sigfredonin/Z80-John-Bell-80-280/image/2732_pinout.png

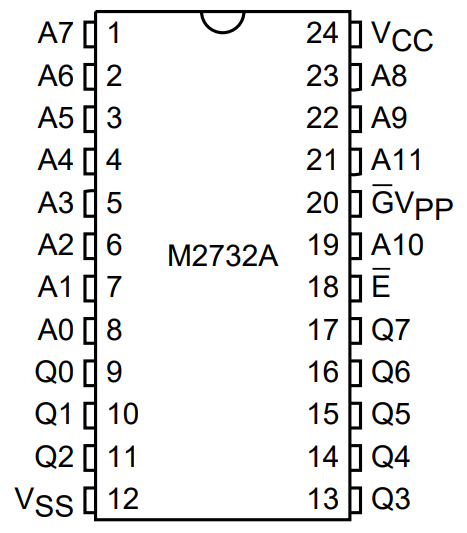
image/2732_pinout.png
