sigfredonin/Z80-John-Bell-80-280/image/7404 Inverter Response to RC Input Circuit.jpg

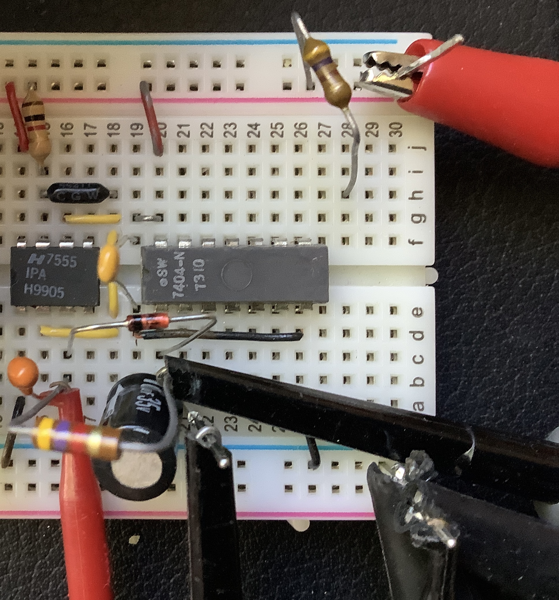
image/7404 Inverter Response to RC Input Circuit.jpg
