sigfredonin/Z80-John-Bell-80-280/image/CD4049AE CMOS Inverter Buffer Response to RC Input.jpg

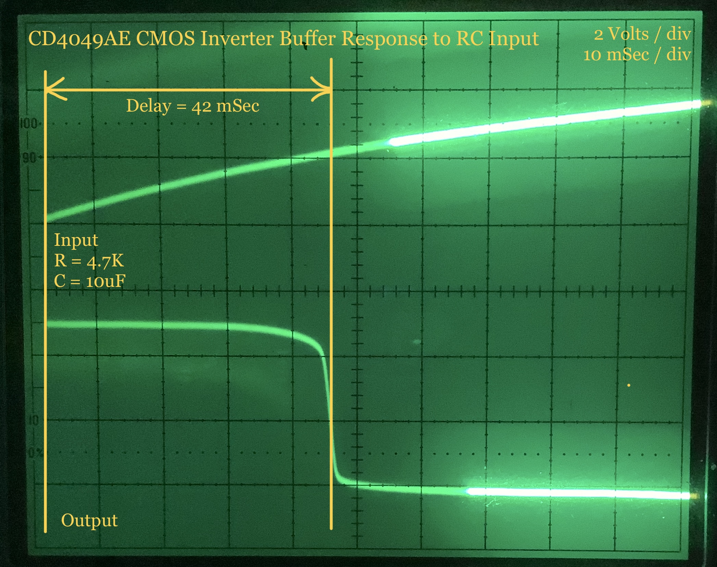
image/CD4049AE CMOS Inverter Buffer Response to RC Input.jpg
