sigfredonin/Z80-John-Bell-80-280/image/EPROM_2716_Reader_schematic.png

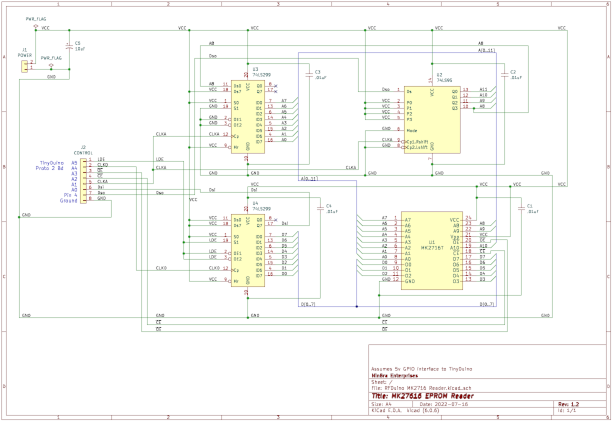
image/EPROM_2716_Reader_schematic.png
