sigfredonin/Z80-John-Bell-80-280/image/John Bell 555 Timer Reset Circuit Response to RC Curve.jpg

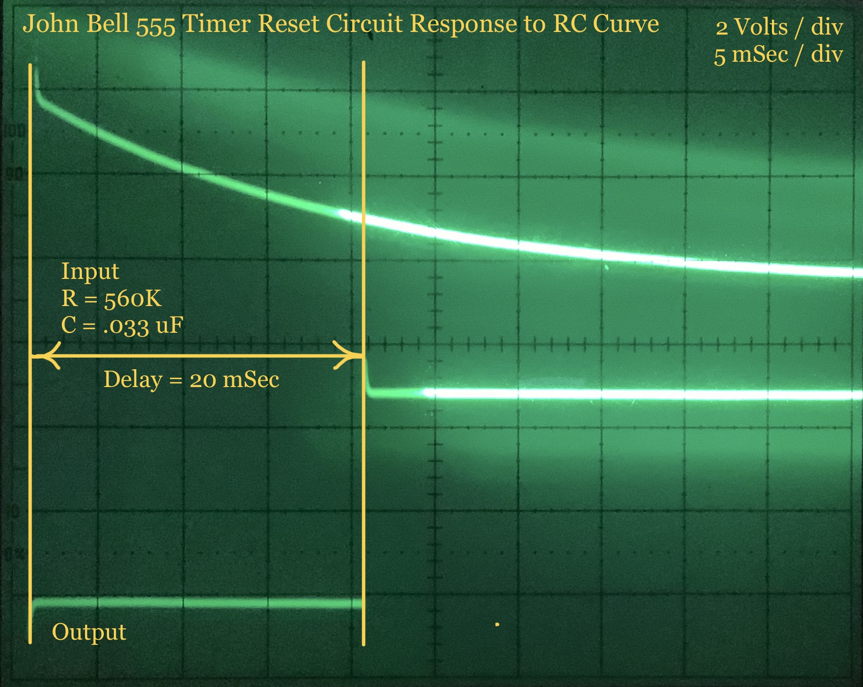
image/John Bell 555 Timer Reset Circuit Response to RC Curve.jpg
