sigfredonin/Z80-John-Bell-80-280/image/Power On Reset - annotated.jpg

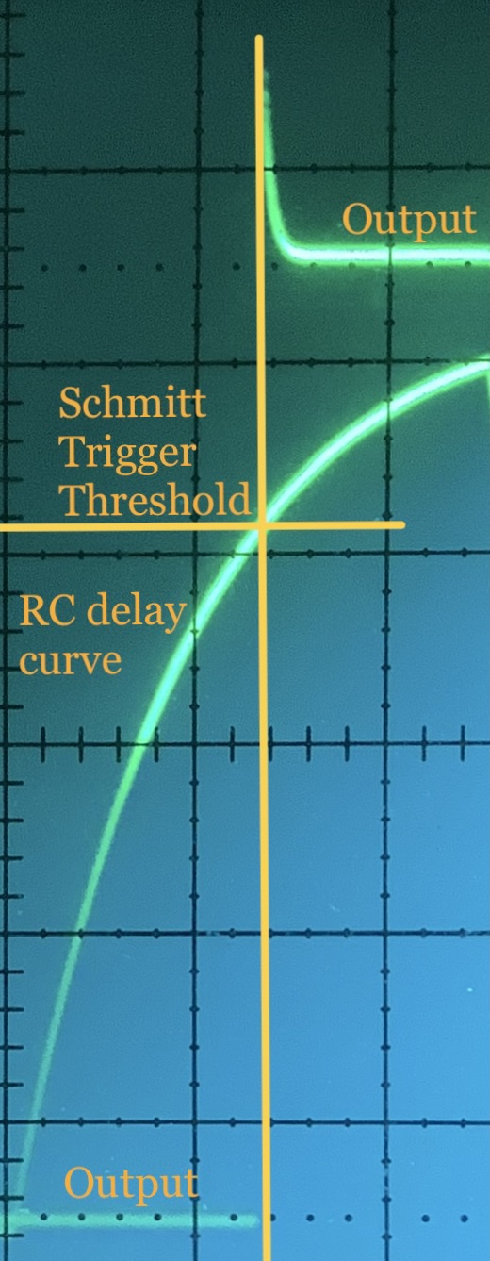
image/Power On Reset - annotated.jpg
