sigfredonin/Z80-John-Bell-80-280/image/TinyDuino 2114 RAM_bb.png

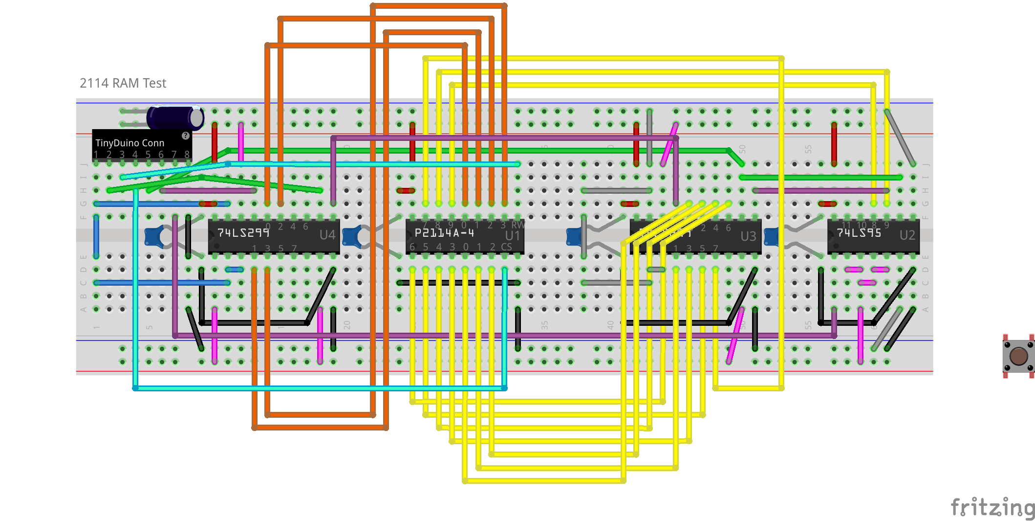
image/TinyDuino 2114 RAM_bb.png
