sigfredonin/Z80-John-Bell-80-280/image/TinyDuino Mk2716 Reader_bb_1.1.png

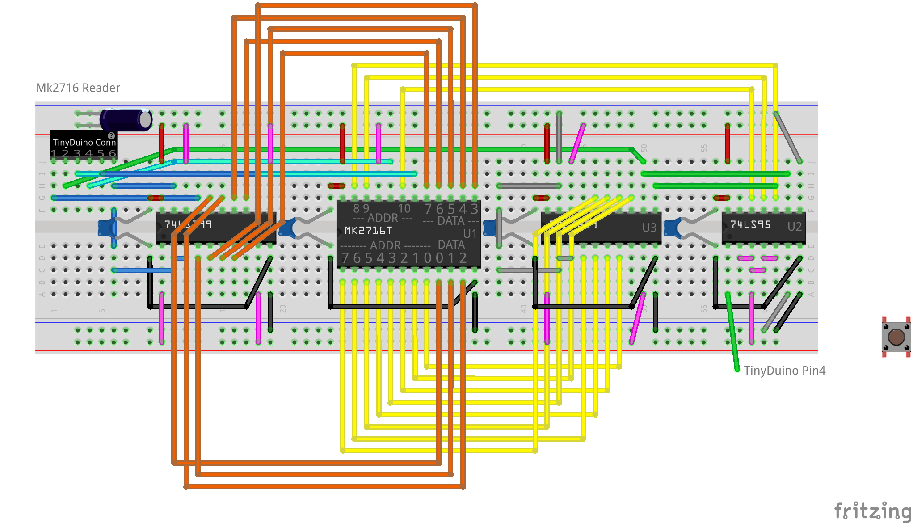
image/TinyDuino Mk2716 Reader_bb_1.1.png
