sigfredonin/Z80-John-Bell-80-280/image/TinyDuino_Processor_Rev_9_coin_cell__front_1800x1800.PNG

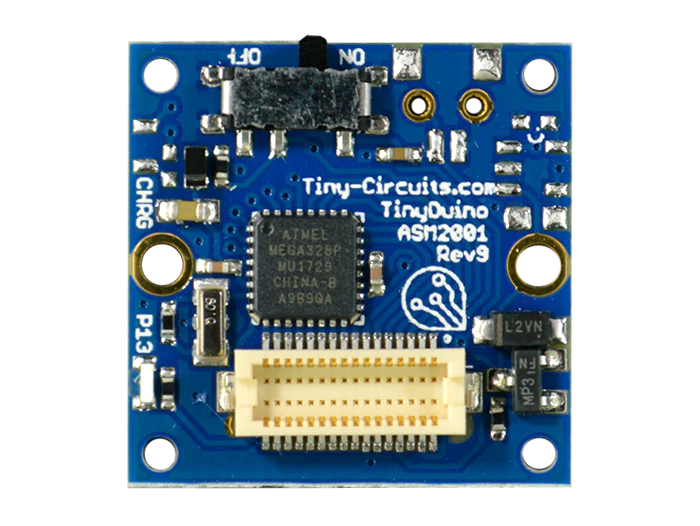
image/TinyDuino_Processor_Rev_9_coin_cell__front_1800x1800.PNG
