sigfredonin/Z80-John-Bell-80-280/image/TinyShield_16_Edge_LED_front_1800x1800.PNG

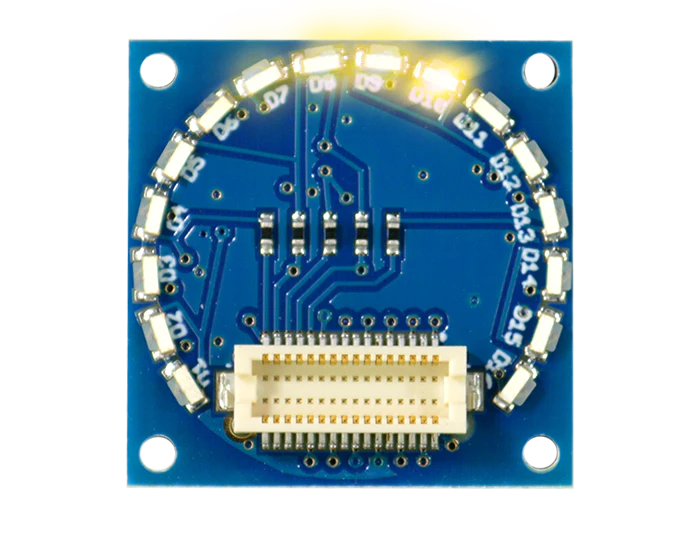
image/TinyShield_16_Edge_LED_front_1800x1800.PNG
