sigfredonin/Z80-John-Bell-80-280/image/TinyShield_Proto_2_back_815x812.PNG

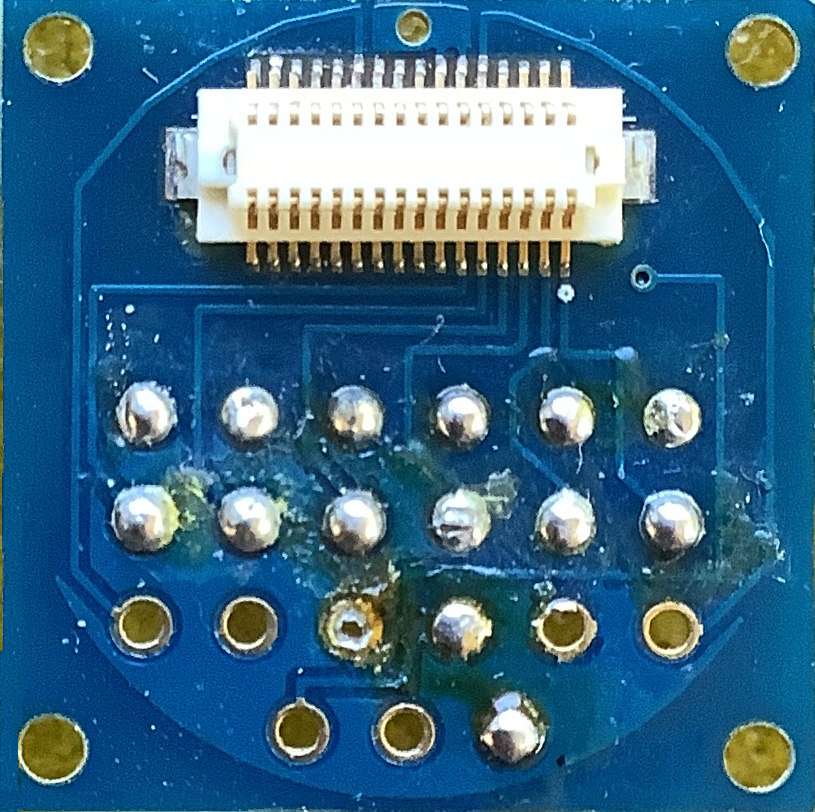
image/TinyShield_Proto_2_back_815x812.PNG
