sigfredonin/Z80-John-Bell-80-280/image/TinyShield_USB_Side_Conn_back_1800x1800.PNG

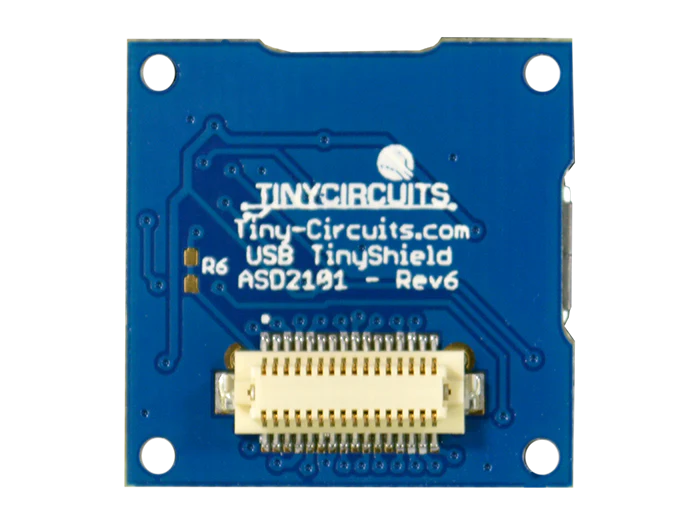
image/TinyShield_USB_Side_Conn_back_1800x1800.PNG
