sigfredonin/Z80-John-Bell-80-280/image/Z80_SBC_Address_Decoding_RAM.png

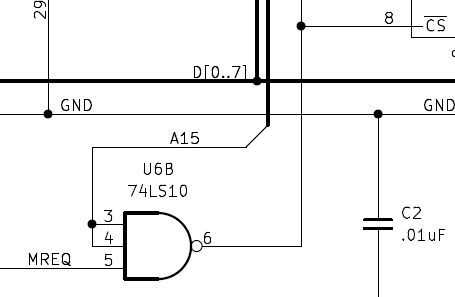
image/Z80_SBC_Address_Decoding_RAM.png
