sigfredonin/Z80-John-Bell-80-280/image/Z80_SBC_PIO_Address_and_Control.PNG

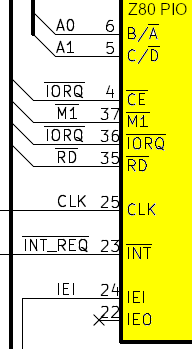
image/Z80_SBC_PIO_Address_and_Control.PNG
