sigfredonin/Z80-John-Bell-80-280/image/Z80_SBC_Solder_Side_Full_Size.JPG

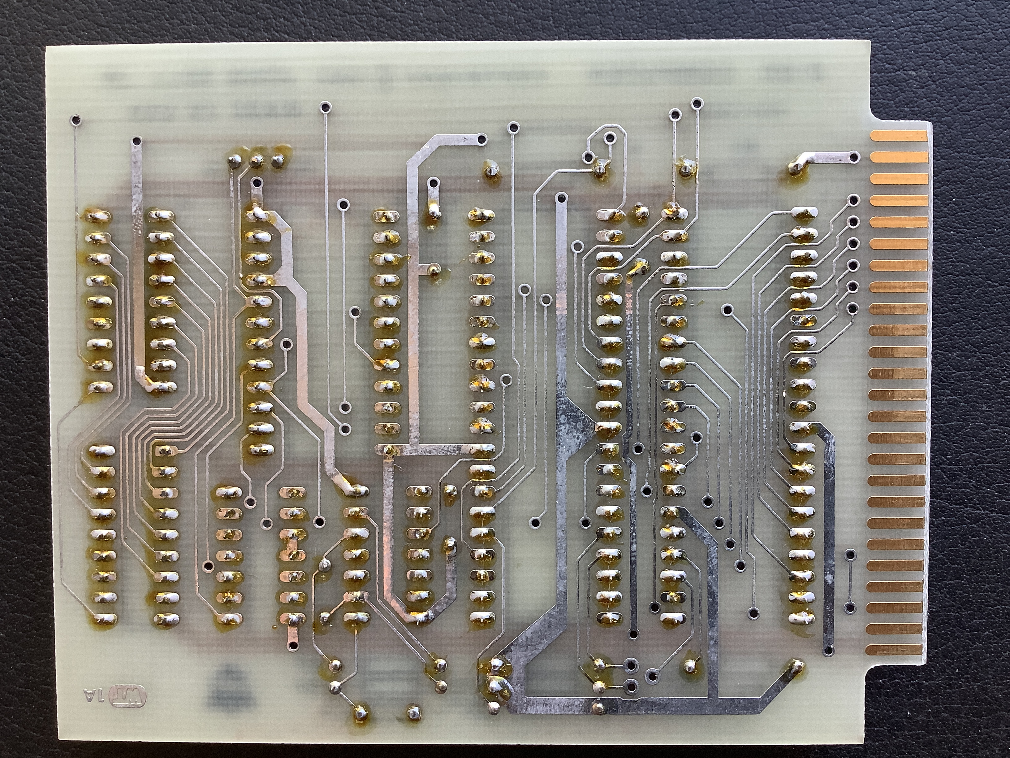
image/Z80_SBC_Solder_Side_Full_Size.JPG
