sigfredonin/Z80-John-Bell-80-280/image/TinyDuino Mk2716 Reader + Unit Tests_bb.png

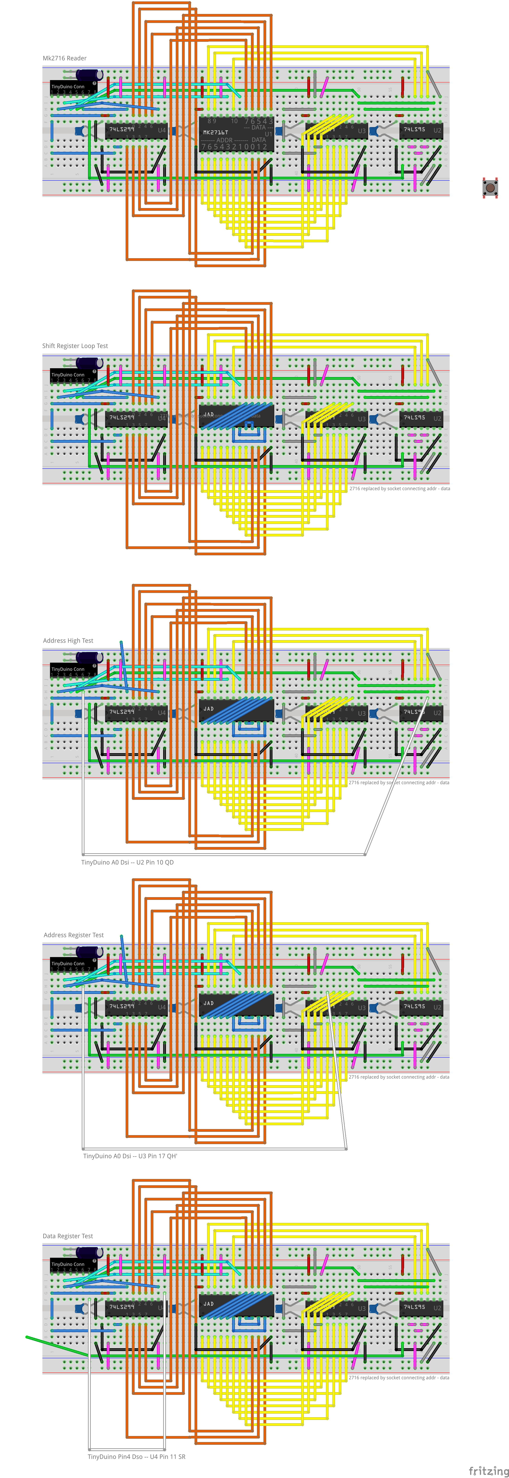
image/TinyDuino Mk2716 Reader + Unit Tests_bb.png
