sigfredonin/Z80-John-Bell-80-280/image/TinyDuino Mk2716 Reader - Shift Register Test_bb_1.3.png

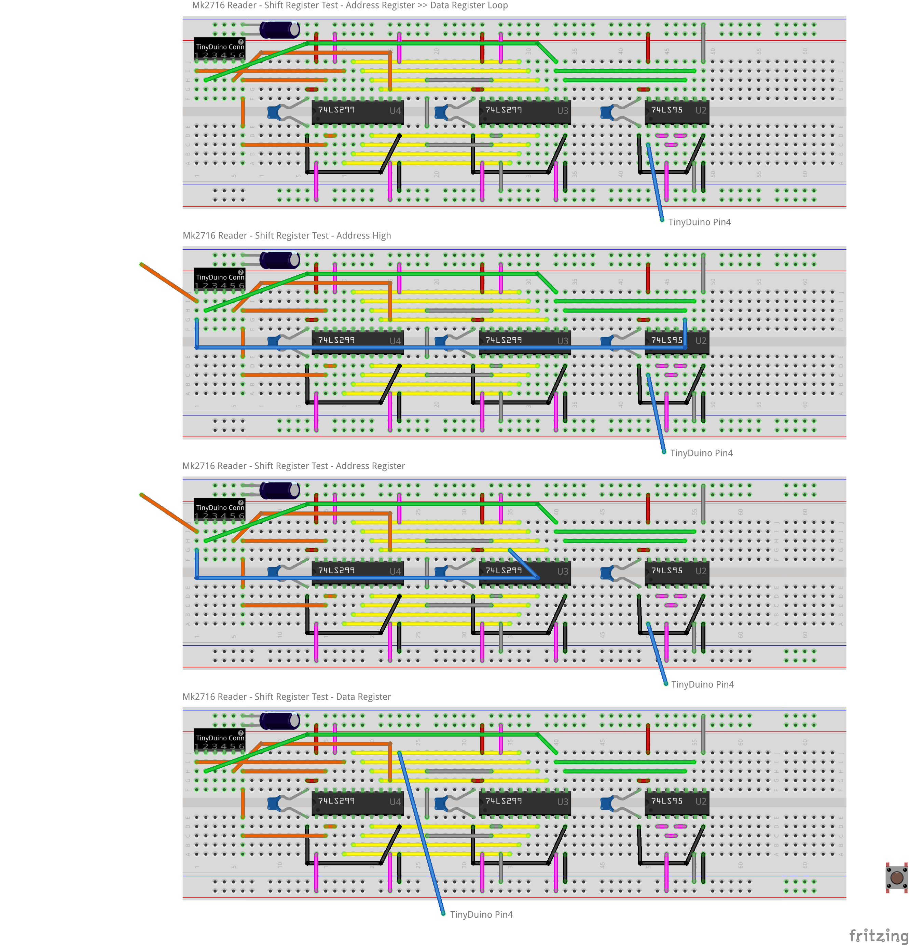
image/TinyDuino Mk2716 Reader - Shift Register Test_bb_1.3.png
