sigfredonin/Z80-John-Bell-80-280/TinyDuino MK2716 Reader - Shift Register Test/TinyDuino MK2716 Reader - Shift Register Test.kicad_sch

## KiCad design TinyDuino MK2716 Reader - Shift Register Test/TinyDuino MK2716 Reader - Shift Register Test.kicad_sch (2022-08-19)

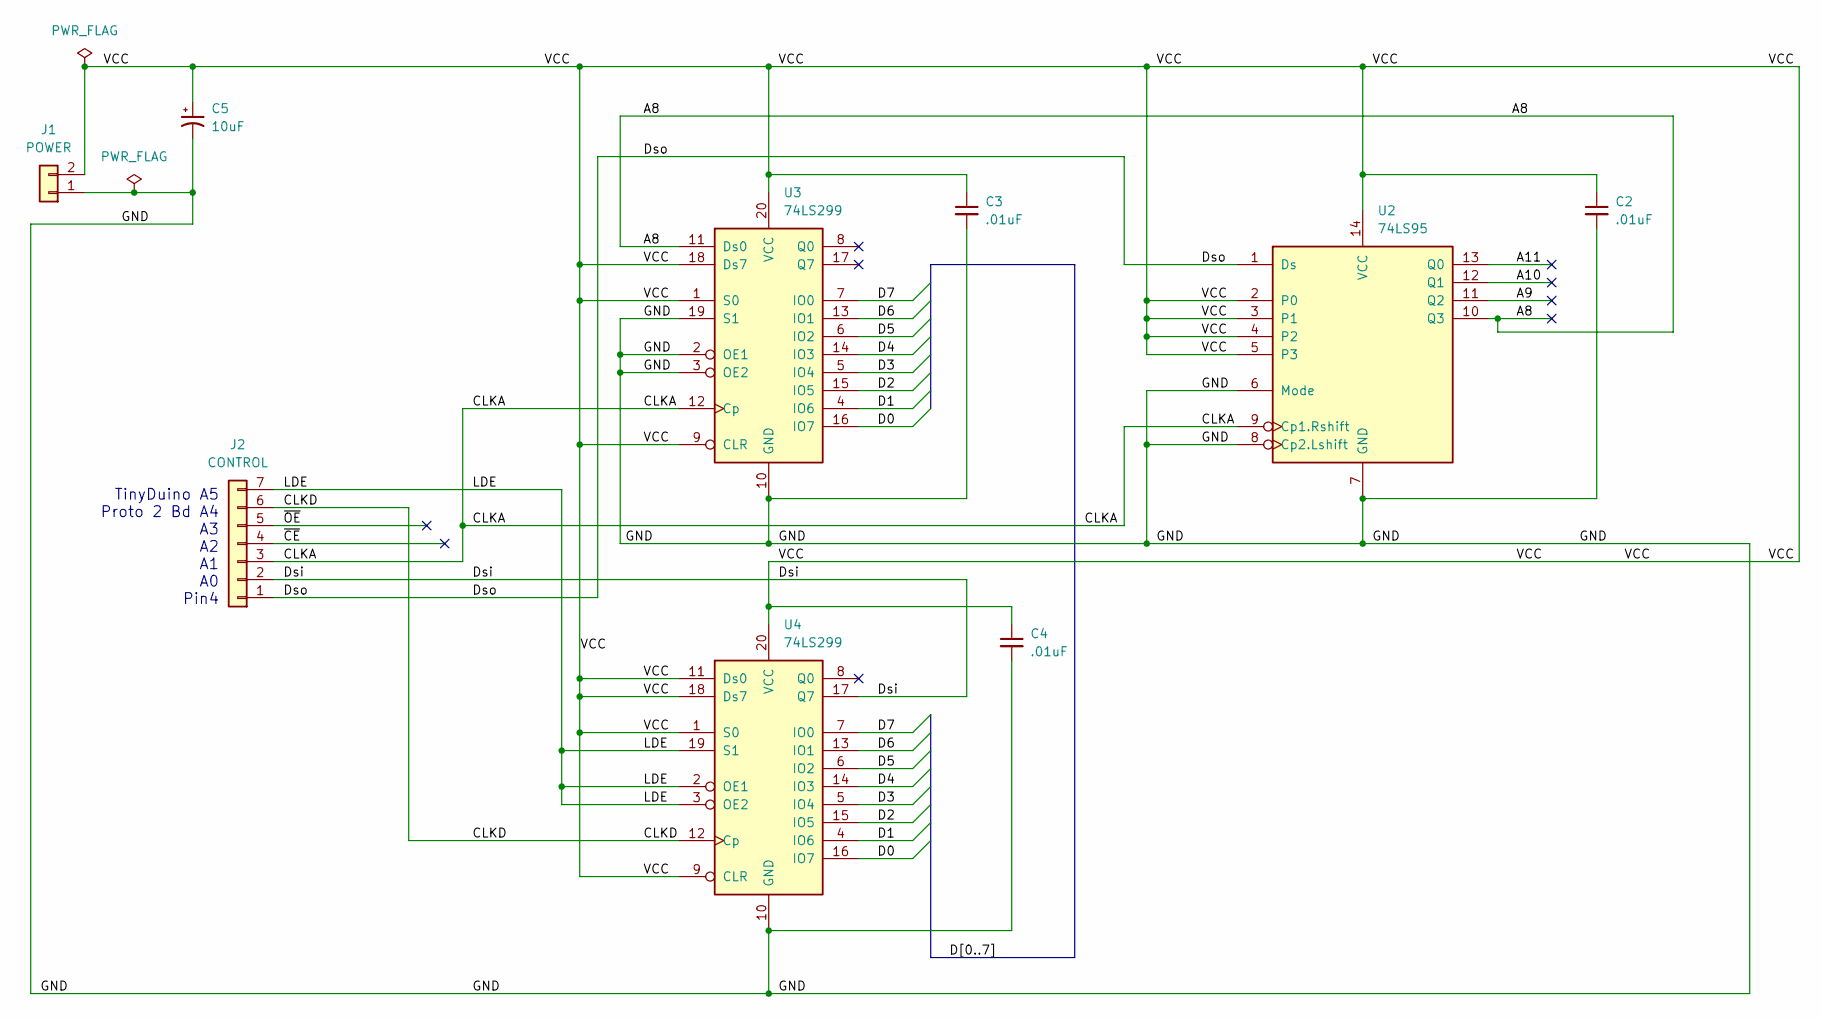
[picture p59: schematic TinyDuino MK2716 Reader - Shift Register Test.kicad_sch]

Parts:
C2, C3, C4: .01uF
C5: 10uF
J1: POWER; PinHeader_1x02_P1.00mm_Horizontal
J2: CONTROL; PinSocket_1x06_P2.54mm_Vertical
U2: 74LS95
U3, U4: 74LS299

Connections:
A8: U2.10 (Q3), U3.11 (Ds0)
A9: U2.11 (Q2)
A10: U2.12 (Q1)
A11: U2.13 (Q0)
CLKA: J2.3, U2.9 (Cp1.Rshift), U3.12 (Cp)
CLKD: J2.6, U4.12 (Cp)
D0: U3.16 (IO7), U4.16 (IO7)
D1: U3.4 (IO6), U4.4 (IO6)
D2: U3.15 (IO5), U4.15 (IO5)
D3: U3.5 (IO4), U4.5 (IO4)
D4: U3.14 (IO3), U4.14 (IO3)
D5: U3.6 (IO2), U4.6 (IO2)
D6: U3.13 (IO1), U4.13 (IO1)
D7: U3.7 (IO0), U4.7 (IO0)
Dsi: J2.2, U4.17 (Q7)
Dso: J2.1, U2.1 (Ds)
GND: C2.2, C3.2, C4.2, C5.2, J1.1, U2.6 (Mode), U2.7 (GND), U2.8 (Cp2.Lshift), U3.2 (OE1), U3.3 (OE2), U3.10 (GND), U3.19 (S1), U4.10 (GND)
LDE: J2.7, U4.2 (OE1), U4.3 (OE2), U4.19 (S1)
VCC: C2.1, C3.1, C4.1, C5.1, J1.2, U2.2 (P0), U2.3 (P1), U2.4 (P2), U2.5 (P3), U2.14 (VCC), U3.1 (S0), U3.9 (CLR), U3.18 (Ds7), U3.20 (VCC), U4.1 (S0), U4.9 (CLR), U4.11 (Ds0), U4.18 (Ds7), U4.20 (VCC)
~CE: J2.4
~OE: J2.5

Notes on the sheet:
TinyDuino A5 Proto 2 Bd A4 A3 A2 A1 A0 Pin4
