sigfredonin/Z80-John-Bell-80-280/z-80_Computer_John_Bell_80-280-Reset/z-80_Computer_John_Bell_80-280-Reset.kicad_sch

## KiCad design z-80_Computer_John_Bell_80-280-Reset/z-80_Computer_John_Bell_80-280-Reset.kicad_sch (2022-08-19)

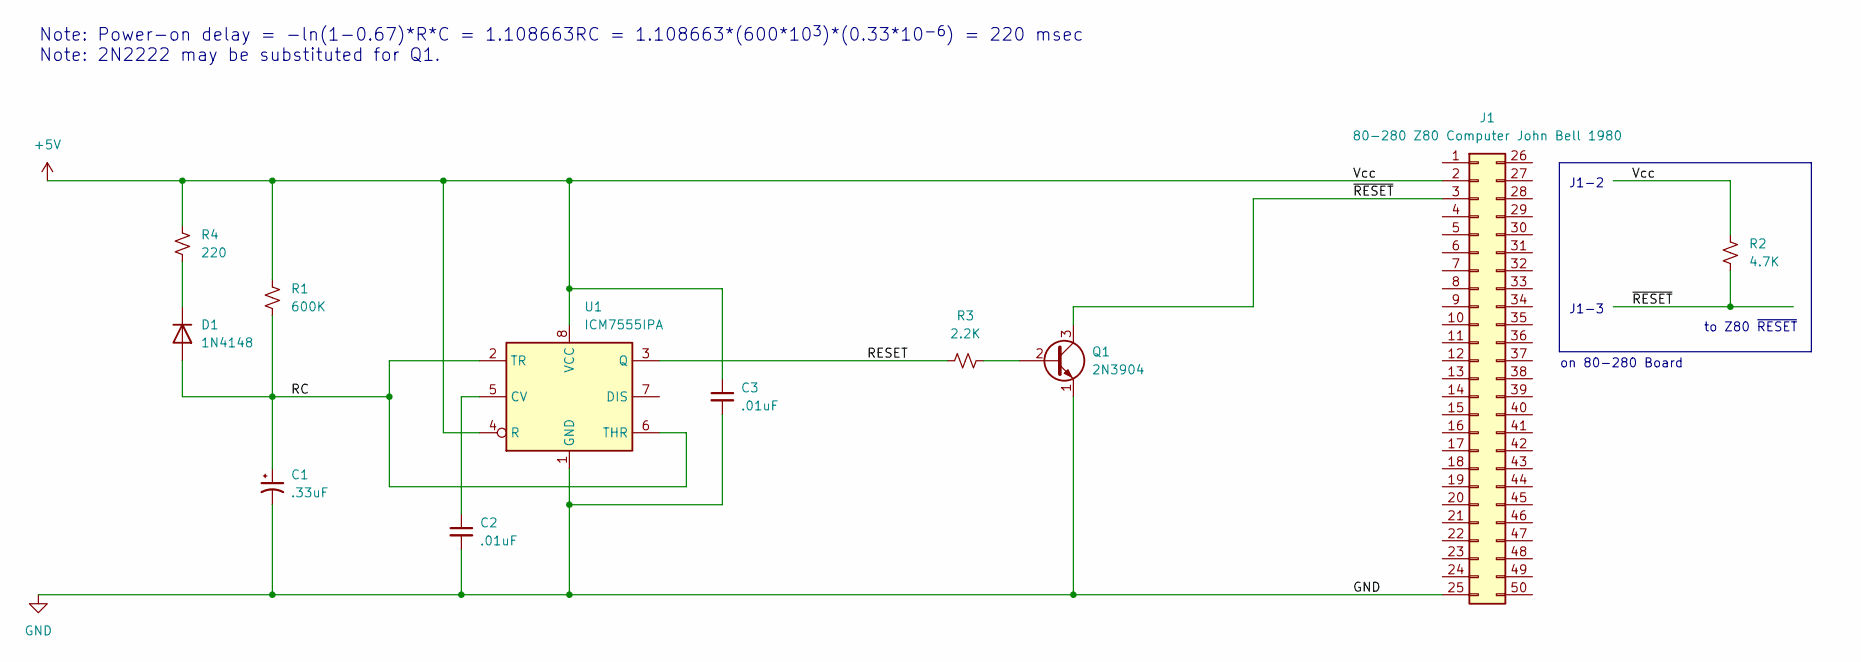
[picture p61: schematic z-80_Computer_John_Bell_80-280-Reset.kicad_sch]

Parts:
C1: .33uF
C2, C3: .01uF
D1: 1N4148; D_DO-35_SOD27_P7.62mm_Horizontal
J1: 80-280 Z80 Computer John Bell 1980
Q1: 2N3904; TO-92_Inline
R1: 600K
R2: 4.7K
R3: 2.2K
R4: 220
U1: ICM7555IPA; DIP-8_W7.62mm

Connections:
GND: C1.2, C2.2, C3.2, J1.25, Q1.1 (E), U1.1 (GND)
unnamed: C2.1, U1.5 (CV)
unnamed: D1.1 (K), R4.1
unnamed: Q1.2 (B), R3.2
RC: C1.1, D1.2 (A), R1.1, U1.2 (TR), U1.6 (THR)
RESET: R3.1, U1.3 (Q)
Vcc: C3.1, J1.2, R1.2, R2.2, R4.2, U1.4 (R), U1.8 (VCC)
~RESET: J1.3, Q1.3 (C), R2.1

Notes on the sheet:
on 80-280 Board
J1-3
to Z80 ~{RESET}
J1-2
Note: Power-on delay = -ln(1-0.67)*R*C = 1.108663RC = 1.108663*(600*10^{3})*(0.33*10^{-6}) = 220 msec Note: 2N2222 may be substituted for Q1.
