sigfredonin/Z80-John-Bell-80-280/z-80_Computer_John_Bell_80-280/z-80_Computer_John_Bell_80-280.kicad_sch

## KiCad design z-80_Computer_John_Bell_80-280/z-80_Computer_John_Bell_80-280.kicad_sch (2022-08-19)

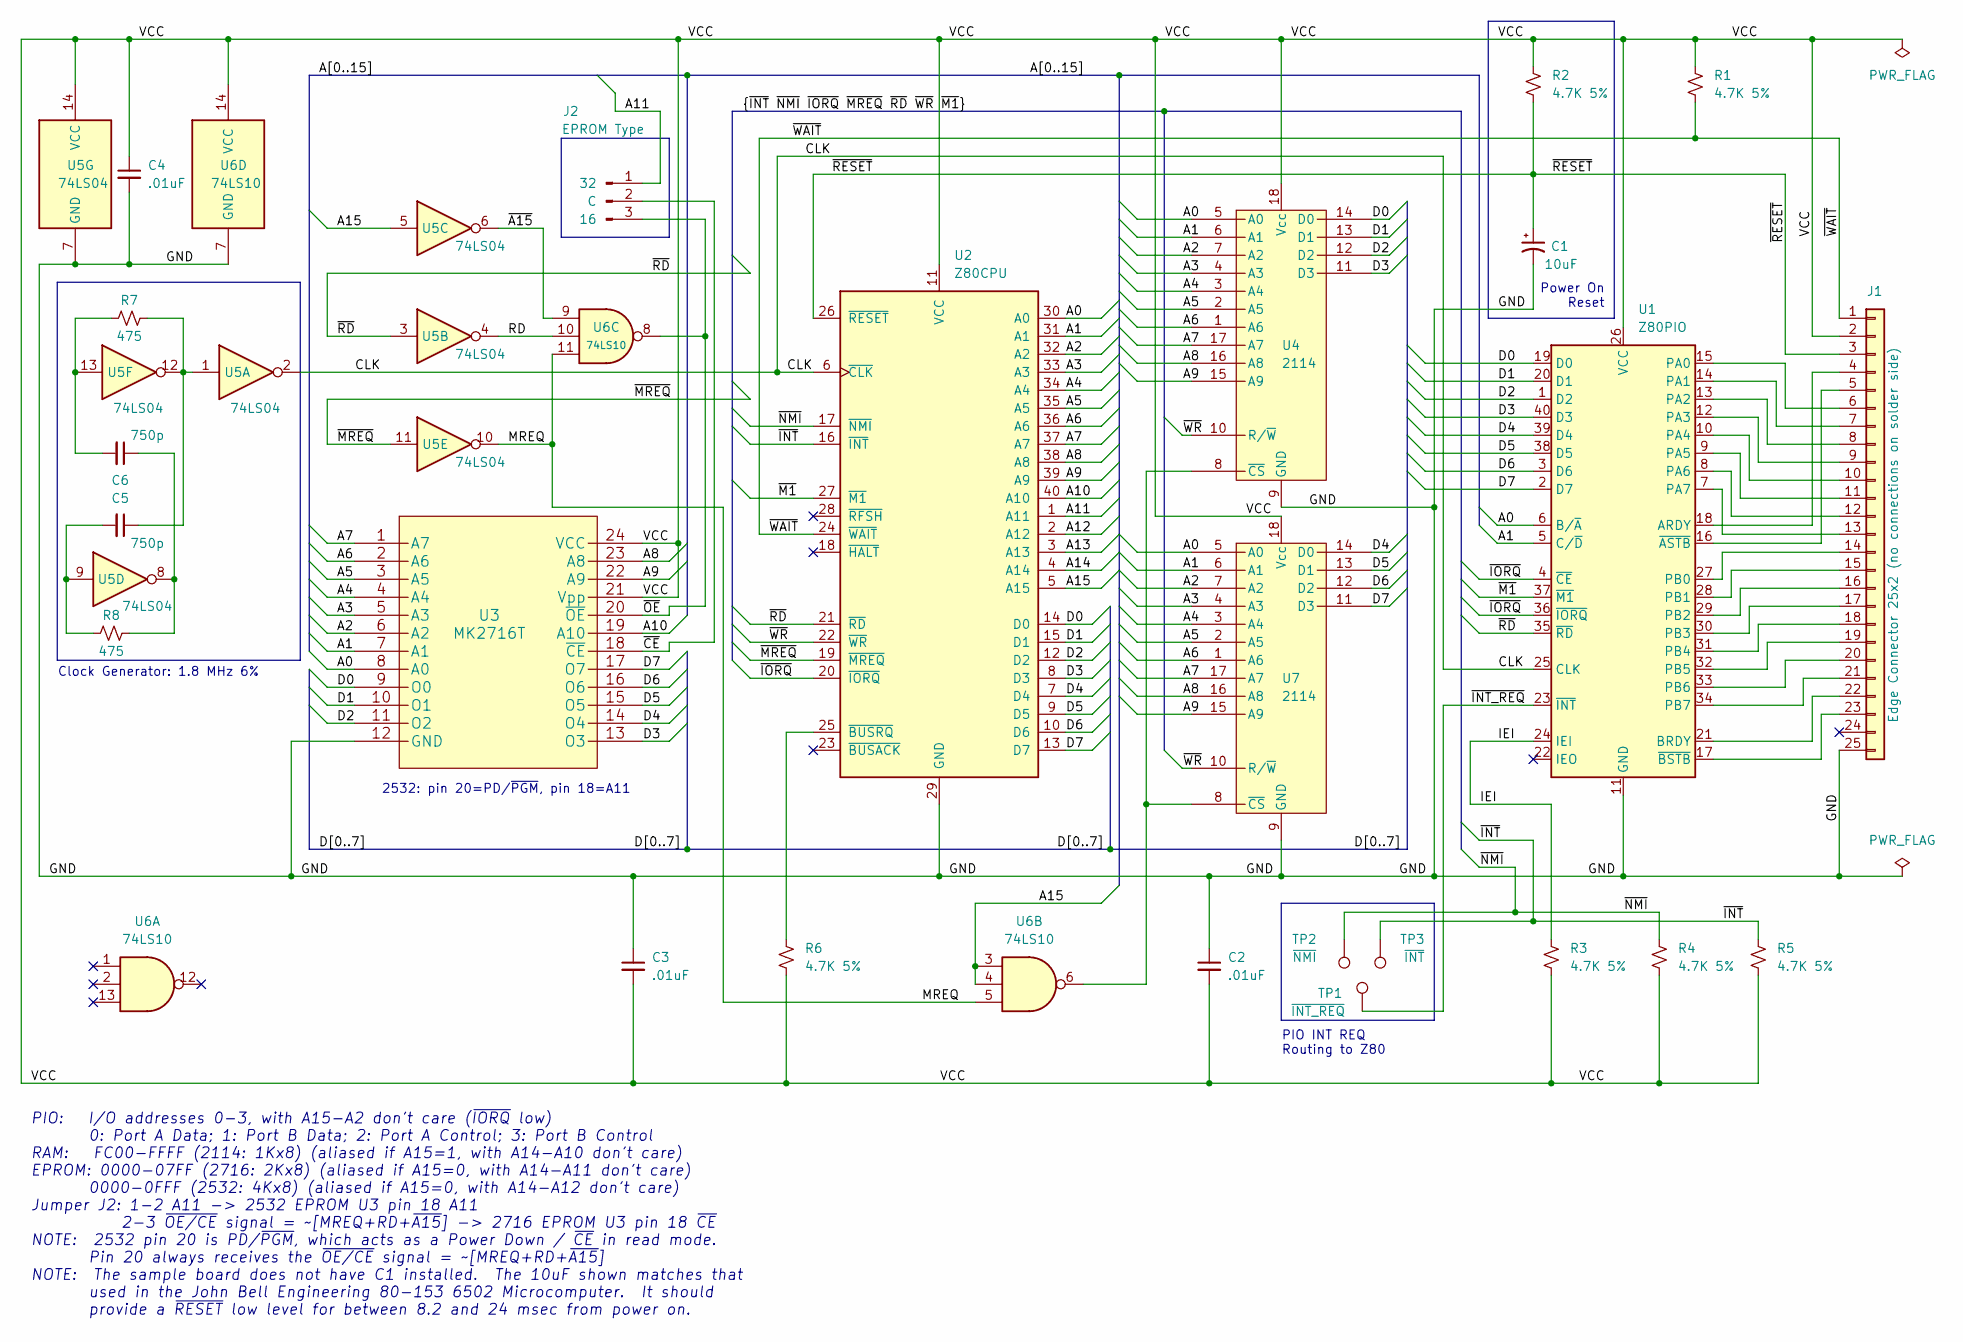
[picture p62: schematic z-80_Computer_John_Bell_80-280.kicad_sch]

Parts:
C1: 10uF
C2, C3, C4: .01uF
C5, C6: 750p
J1: Edge Connector 25x2 (no connections on solder sid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
J2: EPROM Type
R1, R2, R3, R4, R5, R6: 4.7K 5%
R7, R8: 475
TP1: ~{INT_REQ}; TestPoint_Plated_Hole_D2.0mm
TP2: ~{NMI}; TestPoint_Plated_Hole_D2.0mm
TP3: ~{INT}; TestPoint_Plated_Hole_D2.0mm
U1: Z80PIO; DIP-40_W15.24mm
U2: Z80CPU
U3: MK2716T; PDIP24_14P4X32P3_MCH
U4, U7: 2114
U5: 74LS04
U6: 74LS10

Connections:
A0: U1.6 (B/~A), U2.30 (A0), U3.8 (A0), U4.5 (A0), U7.5 (A0)
A1: U1.5 (C/~D), U2.31 (A1), U3.7 (A1), U4.6 (A1), U7.6 (A1)
A2: U2.32 (A2), U3.6 (A2), U4.7 (A2), U7.7 (A2)
A3: U2.33 (A3), U3.5 (A3), U4.4 (A3), U7.4 (A3)
A4: U2.34 (A4), U3.4 (A4), U4.3 (A4), U7.3 (A4)
A5: U2.35 (A5), U3.3 (A5), U4.2 (A5), U7.2 (A5)
A6: U2.36 (A6), U3.2 (A6), U4.1 (A6), U7.1 (A6)
A7: U2.37 (A7), U3.1 (A7), U4.17 (A7), U7.17 (A7)
A8: U2.38 (A8), U3.23 (A8), U4.16 (A8), U7.16 (A8)
A9: U2.39 (A9), U3.22 (A9), U4.15 (A9), U7.15 (A9)
A10: U2.40 (A10), U3.19 (A10)
A11: J2.1, U2.1 (A11)
A12: U2.2 (A12)
A13: U2.3 (A13)
A14: U2.4 (A14)
A15: U2.5 (A15), U5.5, U6.3, U6.4
CLK: U1.25 (CLK), U2.6 (~CLK), U5.2
D0: U1.19 (D0), U2.14 (D0), U3.9 (O0), U4.14 (D0)
D1: U1.20 (D1), U2.15 (D1), U3.10 (O1), U4.13 (D1)
D2: U1.1 (D2), U2.12 (D2), U3.11 (O2), U4.12 (D2)
D3: U1.40 (D3), U2.8 (D3), U3.13 (O3), U4.11 (D3)
D4: U1.39 (D4), U2.7 (D4), U3.14 (O4), U7.14 (D0)
D5: U1.38 (D5), U2.9 (D5), U3.15 (O5), U7.13 (D1)
D6: U1.3 (D6), U2.10 (D6), U3.16 (O6), U7.12 (D2)
D7: U1.2 (D7), U2.13 (D7), U3.17 (O7), U7.11 (D3)
GND: C1.2, C2.1, C3.1, C4.2, J1.25, U1.11 (GND), U2.29 (GND), U3.12 (GND), U4.9 (GND), U5.7 (GND), U6.7 (GND), U7.9 (GND)
IEI: R3.1, U1.24 (IEI)
MREQ: U5.10, U6.5, U6.11
unnamed: C5.1, R7.2, U5.1, U5.12
unnamed: C5.2, R8.1, U5.9
unnamed: C6.1, R8.2, U5.8
unnamed: C6.2, R7.1, U5.13
unnamed: J1.4, U1.18 (ARDY)
unnamed: J1.5, U1.16 (~ASTB)
unnamed: J1.6, U1.15 (PA0)
unnamed: J1.7, U1.14 (PA1)
unnamed: J1.8, U1.13 (PA2)
unnamed: J1.9, U1.12 (PA3)
unnamed: J1.10, U1.10 (PA4)
unnamed: J1.11, U1.9 (PA5)
unnamed: J1.12, U1.8 (PA6)
unnamed: J1.13, U1.7 (PA7)
unnamed: J1.14, U1.27 (PB0)
unnamed: J1.15, U1.28 (PB1)
unnamed: J1.16, U1.29 (PB2)
unnamed: J1.17, U1.30 (PB3)
unnamed: J1.18, U1.31 (PB4)
unnamed: J1.19, U1.32 (PB5)
unnamed: J1.20, U1.33 (PB6)
unnamed: J1.21, U1.34 (PB7)
unnamed: J1.22, U1.21 (BRDY)
unnamed: J1.23, U1.17 (~BSTB)
unnamed: R6.1, U2.25 (~BUSRQ)
unnamed: U4.8 (~CS), U6.6, U7.8 (~CS)
RD: U5.4, U6.10
VCC: C2.2, C3.2, C4.1, J1.2, R1.1, R2.1, R3.2, R4.2, R5.2, R6.2, U1.26 (VCC), U2.11 (VCC), U3.21 (Vpp), U3.24 (VCC), U4.18 (Vcc), U5.14 (VCC), U6.14 (VCC), U7.18 (Vcc)
~A15: U5.6, U6.9
~CE: J2.2, U3.18 (~CE)
~INT_REQ: TP1.1, U1.23 (~INT)
~INT: R5.1, TP3.1, U2.16 (~INT)
~IORQ: U1.4 (~CE), U1.36 (~IORQ), U2.20 (~IORQ)
~M1: U1.37 (~M1), U2.27 (~M1)
~MREQ: U2.19 (~MREQ), U5.11
~NMI: R4.1, TP2.1, U2.17 (~NMI)
~OE: J2.3, U3.20 (~OE), U6.8
~RD: U1.35 (~RD), U2.21 (~RD), U5.3
~RESET: C1.1, J1.3, R2.2, U2.26 (~RESET)
~WAIT: J1.1, R1.2, U2.24 (~WAIT)
~WR: U2.22 (~WR), U4.10 (R/~W), U7.10 (R/~W)

Notes on the sheet:
2532: pin 20=PD/~{PGM}, pin 18=A11
Clock Generator: 1.8 MHz 6%
PIO INT REQ Routing to Z80
PIO: I/O addresses 0-3, with A15-A2 don't care (~{IORQ} low) 0: Port A Data; 1: Port B Data; 2: Port A Control; 3: Port B Control RAM: FC00-FFFF (2114: 1Kx8) (aliased if A15=1, with A14-A10 don't care) EPROM: 0000-07FF (2716: 2Kx8) (aliased if A15=0, with A14-A11 don't care) 0000-0FFF (2532: 4Kx8) 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
Power On Reset
